splitkb/kyria/High Profile Case/0.10mm Kerf/04 Hi pro 1.dxf

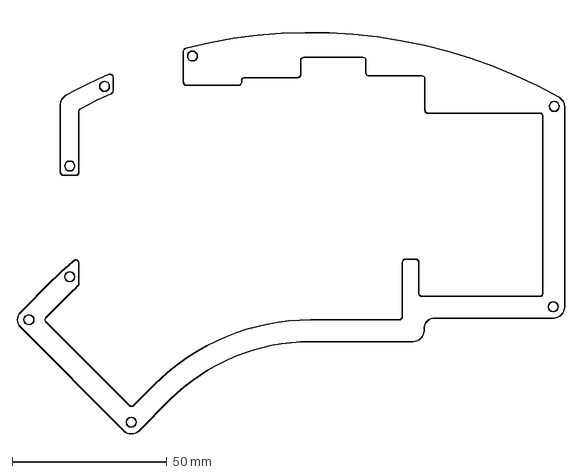
[picture p17: CAD file, 2019-12-01]
High Profile Case/0.10mm Kerf/04 Hi pro 1.dxf
177.0 x 135.2 mm
