splitkb/kyria/rev1 and rev2/3D Printed Case/case files/switch_plate.stl

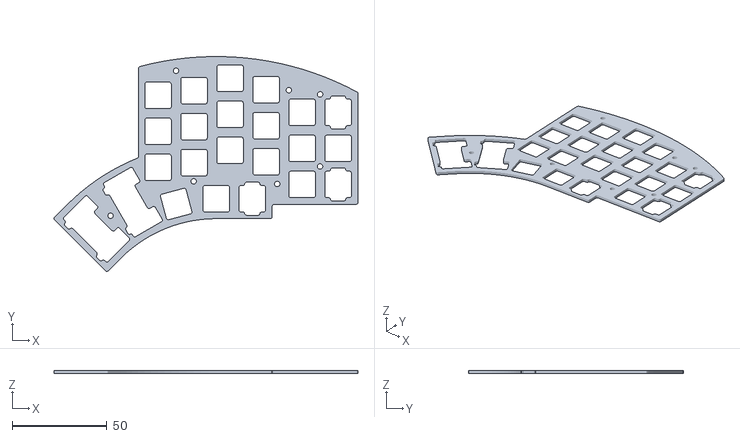
[picture p18: CAD file, 2020-11-22]
rev1 and rev2/3D Printed Case/case files/switch_plate.stl
160.8 x 113.7 x 1.70
