splitkb/kyria/rev1 and rev2/Plate Case/Kyria Plate Case Top - 5 columns - 0.1mm Kerf.dxf

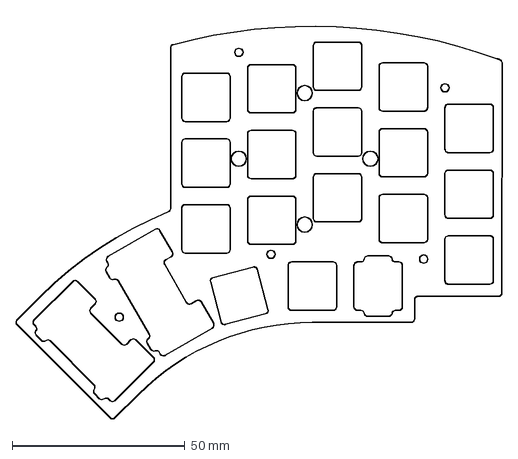
[picture p20: CAD file, 2022-07-19]
rev1 and rev2/Plate Case/Kyria Plate Case Top - 5 columns - 0.1mm Kerf.dxf
140.7 x 116.6 mm
