splitkb/kyria/rev3/Kyria rev3 Top Plate - No Puck - 0.1mm Kerf.dxf

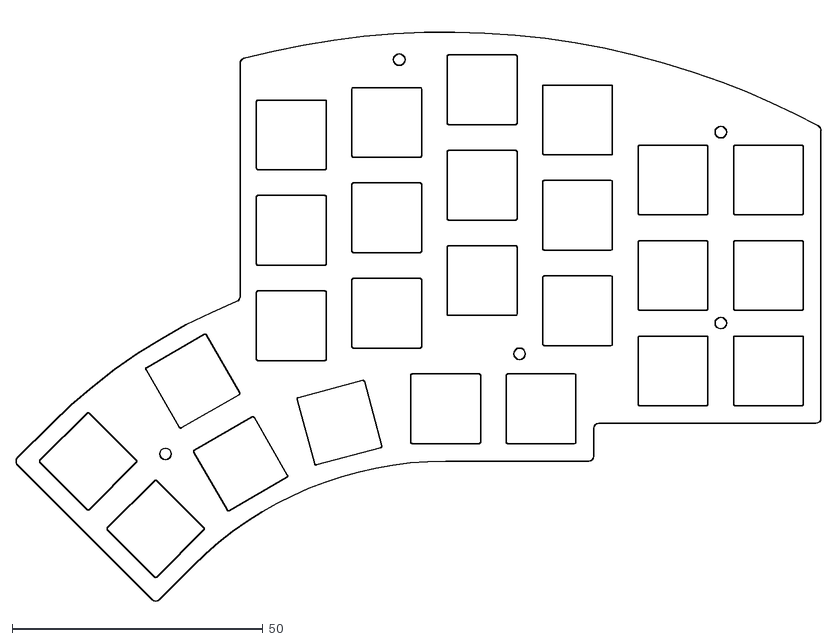
[picture p21: CAD file, 2023-04-05]
rev3/Kyria rev3 Top Plate - No Puck - 0.1mm Kerf.dxf
160.7 x 116.8
