splitkb/kyria/rev3/Kyria rev3 Bottom Plate - Puck - No Kerf.dxf

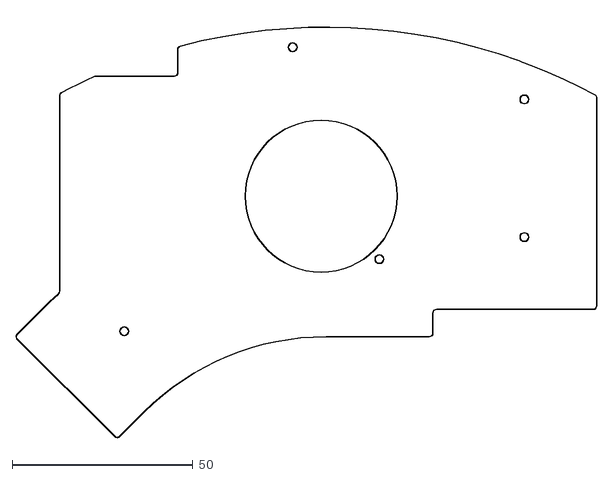
[picture p22: CAD file, 2023-04-05]
rev3/Kyria rev3 Bottom Plate - Puck - No Kerf.dxf
160.8 x 116.6
