splitkb/kyria/rev1 and rev2/High Profile Case/Kyria HiPro Case Top 1 - No Kerf.dxf

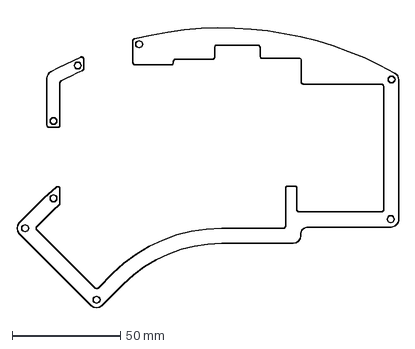
[picture p23: CAD file, 2020-11-22]
rev1 and rev2/High Profile Case/Kyria HiPro Case Top 1 - No Kerf.dxf
177.0 x 135.2 mm
