splitkb/kyria/rev1 and rev2/Plate Case/Kyria Plate Case Bottom - 5 columns - No Puck - No Kerf.dxf

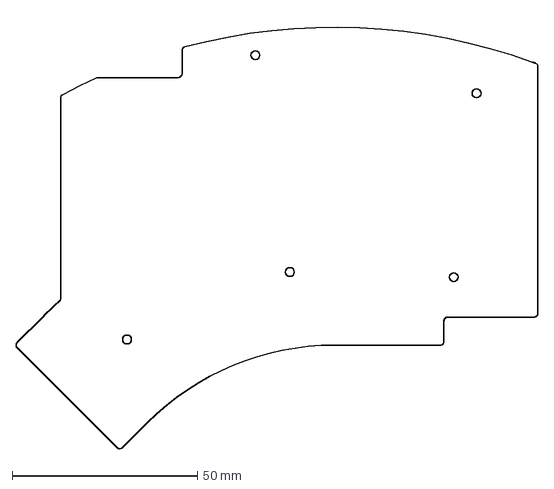
[picture p24: CAD file, 2020-11-22]
rev1 and rev2/Plate Case/Kyria Plate Case Bottom - 5 columns - No Puck - No Kerf.dxf
140.7 x 116.6 mm
