splitkb/kyria/rev1 and rev2/High Profile Case/Kyria HiPro Case Top 2 - 0.1mm Kerf.dxf

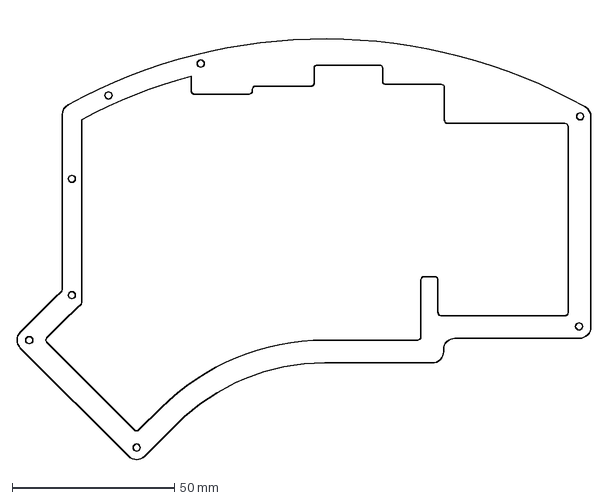
[picture p26: CAD file, 2020-11-22]
rev1 and rev2/High Profile Case/Kyria HiPro Case Top 2 - 0.1mm Kerf.dxf
177.0 x 136.9 mm
