splitkb/kyria/rev1 and rev2/Plate Case/Kyria Plate Case Bottom - 5 columns - No Puck - 0.1mm Kerf.dxf

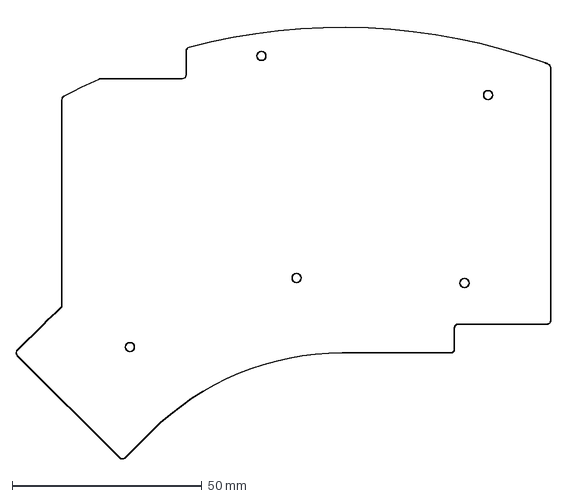
[picture p30: CAD file, 2020-11-22]
rev1 and rev2/Plate Case/Kyria Plate Case Bottom - 5 columns - No Puck - 0.1mm Kerf.dxf
140.7 x 116.6 mm
