splitkb/kyria/rev3/Kyria rev3 Bottom Plate - 0.1mm Kerf.dxf

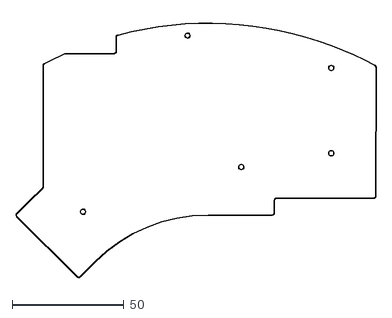
[picture p31: CAD file, 2023-04-05]
rev3/Kyria rev3 Bottom Plate - 0.1mm Kerf.dxf
160.8 x 116.8
