splitkb/kyria/rev1 and rev2/High Profile Case/Kyria HiPro Case Base - No Puck - 0.1mm Kerf.dxf

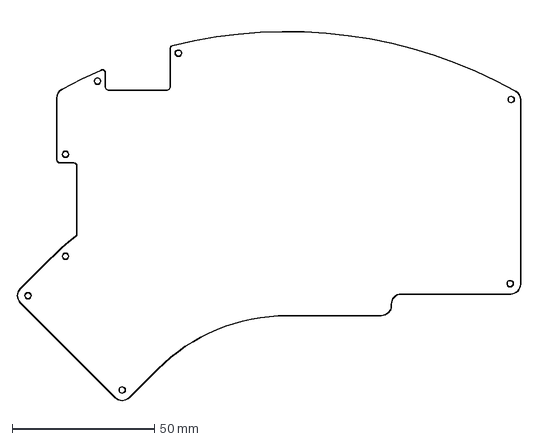
[picture p32: CAD file, 2020-11-22]
rev1 and rev2/High Profile Case/Kyria HiPro Case Base - No Puck - 0.1mm Kerf.dxf
177.0 x 135.2 mm
