splitkb/kyria/rev1 and rev2/Plate Case/Kyria Plate Case Bottom - 6 columns - Puck - 0.1mm Kerf.dxf

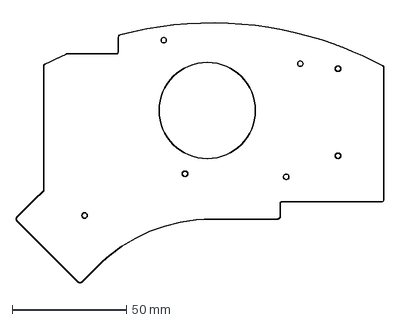
[picture p33: CAD file, 2020-11-22]
rev1 and rev2/Plate Case/Kyria Plate Case Bottom - 6 columns - Puck - 0.1mm Kerf.dxf
160.8 x 116.6 mm
