splitkb/kyria/rev1 and rev2/High Profile Case/Kyria HiPro Top 2 Integrated Guard - 0.1mm Kerf.dxf

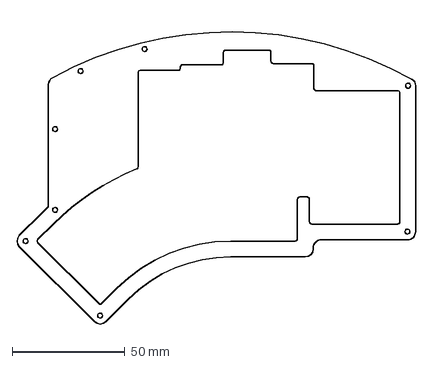
[picture p35: CAD file, 2020-11-22]
rev1 and rev2/High Profile Case/Kyria HiPro Top 2 Integrated Guard - 0.1mm Kerf.dxf
177.0 x 136.9 mm
