splitkb/kyria/rev1 and rev2/Plate Case/Kyria Plate Case Top - 6 columns - 0.1mm Kerf.dxf

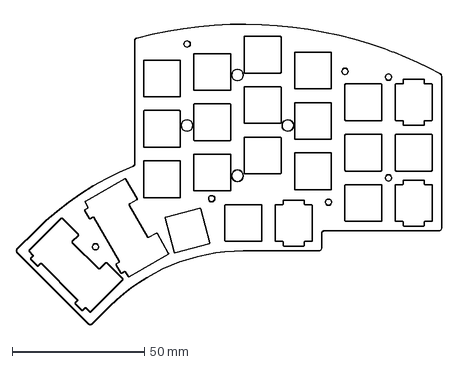
[picture p36: CAD file, 2020-11-22]
rev1 and rev2/Plate Case/Kyria Plate Case Top - 6 columns - 0.1mm Kerf.dxf
160.8 x 116.6 mm
