splitkb/kyria/rev3/Kyria rev3 OLED Cover - 0.1mm Kerf.dxf

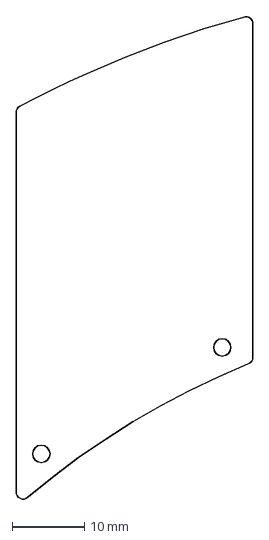
[picture p37: CAD file, 2020-11-22]
rev3/Kyria rev3 OLED Cover - 0.1mm Kerf.dxf
32.8 x 66.8 mm
