splitkb/kyria/rev1 and rev2/High Profile Case/Kyria HiPro Case Base - No Puck - No Kerf.dxf

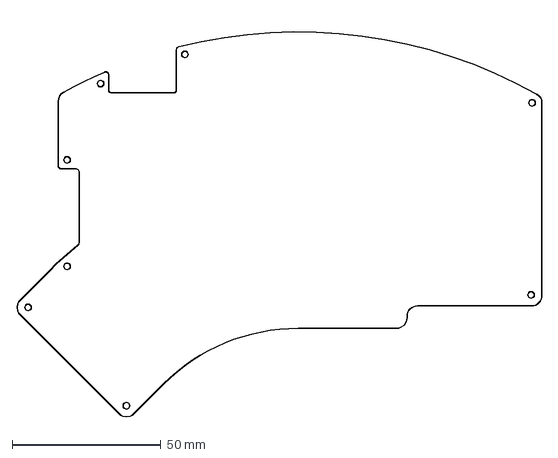
[picture p38: CAD file, 2020-11-22]
rev1 and rev2/High Profile Case/Kyria HiPro Case Base - No Puck - No Kerf.dxf
177.0 x 135.2 mm
