splitkb/kyria/rev1 and rev2/Plate Case/Kyria Plate Case Bottom - 6 columns - No Puck - No Kerf.dxf

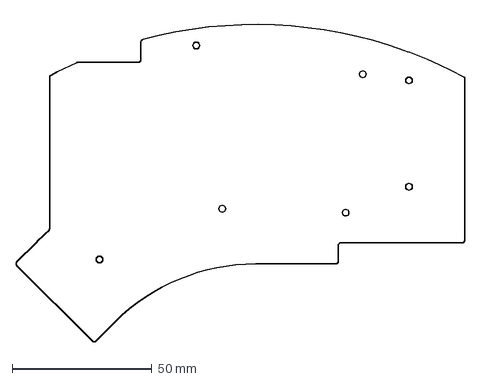
[picture p39: CAD file, 2020-11-22]
rev1 and rev2/Plate Case/Kyria Plate Case Bottom - 6 columns - No Puck - No Kerf.dxf
160.8 x 116.6 mm
