splitkb/kyria/rev1 and rev2/High Profile Case/Kyria HiPro Top 2 Integrated Guard - No Kerf.dxf

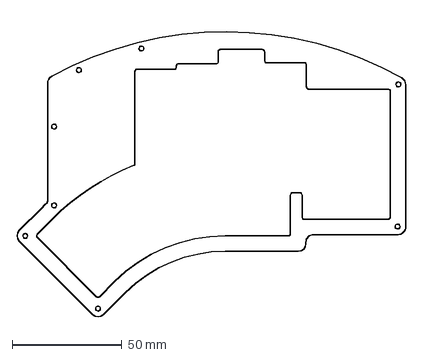
[picture p40: CAD file, 2020-11-22]
rev1 and rev2/High Profile Case/Kyria HiPro Top 2 Integrated Guard - No Kerf.dxf
177.0 x 136.9 mm
