splitkb/kyria/rev1 and rev2/High Profile Case/Kyria HiPro Case Plate - ALPS - No Puck - 0.1mm Kerf.dxf

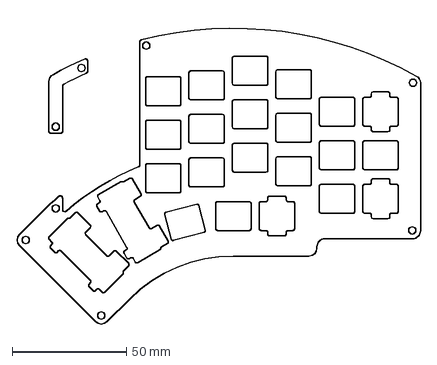
[picture p42: CAD file, 2019-12-01]
rev1 and rev2/High Profile Case/Kyria HiPro Case Plate - ALPS - No Puck - 0.1mm Kerf.dxf
177.0 x 135.2 mm
