splitkb/kyria/rev1 and rev2/High Profile Case/Kyria HiPro Case Plate - ALPS - No Puck - No Kerf.dxf

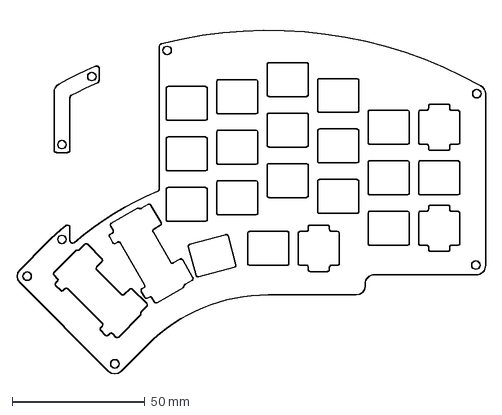
[picture p43: CAD file, 2019-12-01]
rev1 and rev2/High Profile Case/Kyria HiPro Case Plate - ALPS - No Puck - No Kerf.dxf
177.0 x 135.2 mm
