splitkb/kyria/rev1 and rev2/Plate Case/Kyria Plate Case Top ALPS - 6 columns - No Puck - 0.1mm Kerf.dxf

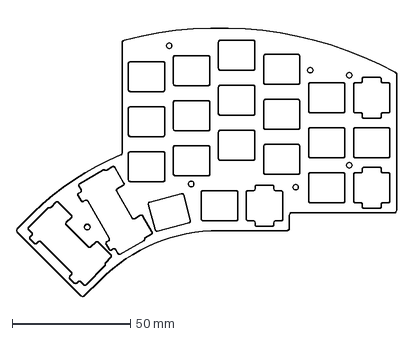
[picture p44: CAD file, 2019-12-01]
rev1 and rev2/Plate Case/Kyria Plate Case Top ALPS - 6 columns - No Puck - 0.1mm Kerf.dxf
160.9 x 118.8 mm
