splitkb/kyria/rev1 and rev2/High Profile Case/Kyria HiPro Guard - No Kerf.dxf

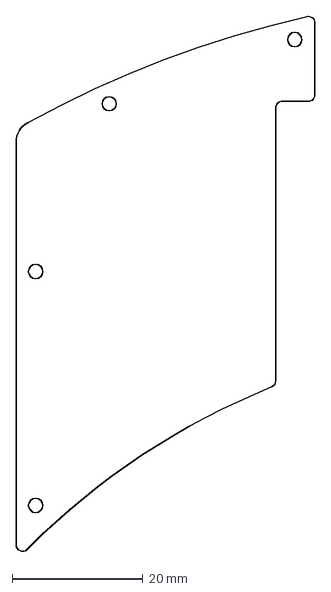
[picture p45: CAD file, 2019-09-16]
rev1 and rev2/High Profile Case/Kyria HiPro Guard - No Kerf.dxf
45.8 x 82.0 mm
