splitkb/kyria/rev1 and rev2/Plate Case/Kyria Plate Case Top ALPS - 6 columns - No Puck - No Kerf.dxf

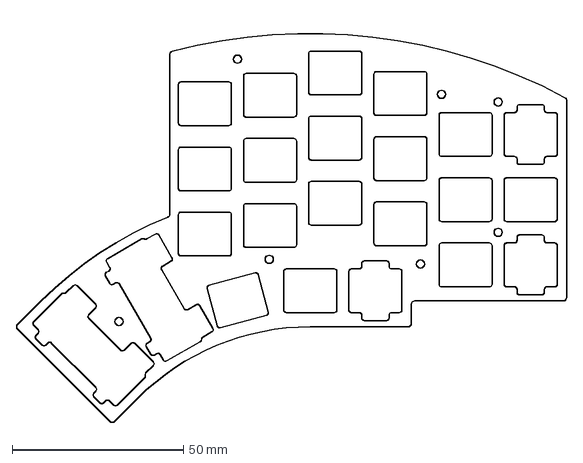
[picture p46: CAD file, 2019-12-01]
rev1 and rev2/Plate Case/Kyria Plate Case Top ALPS - 6 columns - No Puck - No Kerf.dxf
160.9 x 118.8 mm
